udellc/OptronMini/pics/Installation/02b.MaxProj.gif

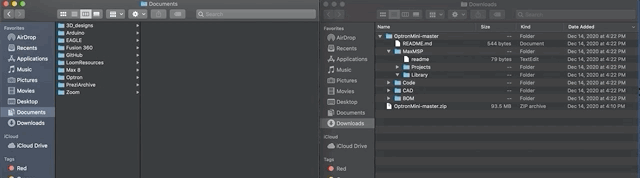
pics/Installation/02b.MaxProj.gif
